JeanRenier/Remoting-a-microBIT-X/pictures/home_receiving.jpg

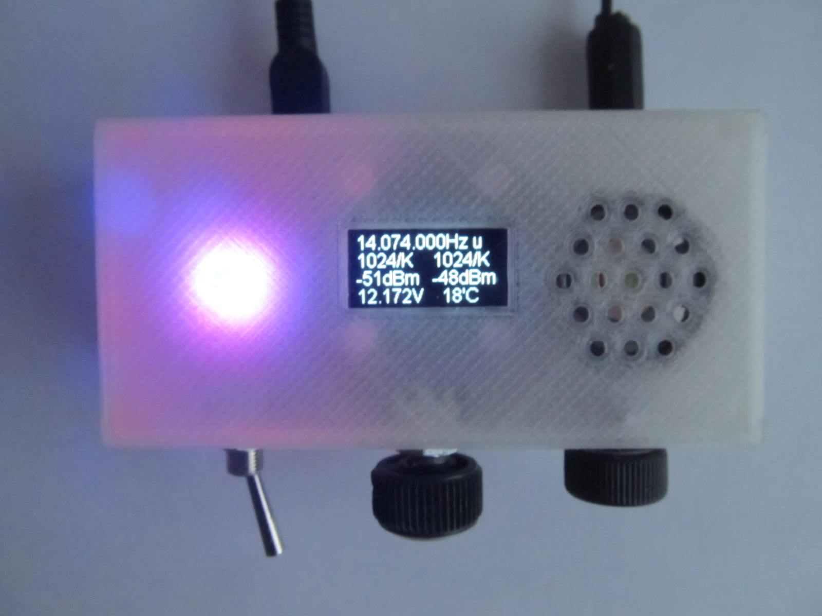
pictures/home_receiving.jpg
