JeanRenier/Remoting-a-microBIT-X/pictures/remote_housing.jpg

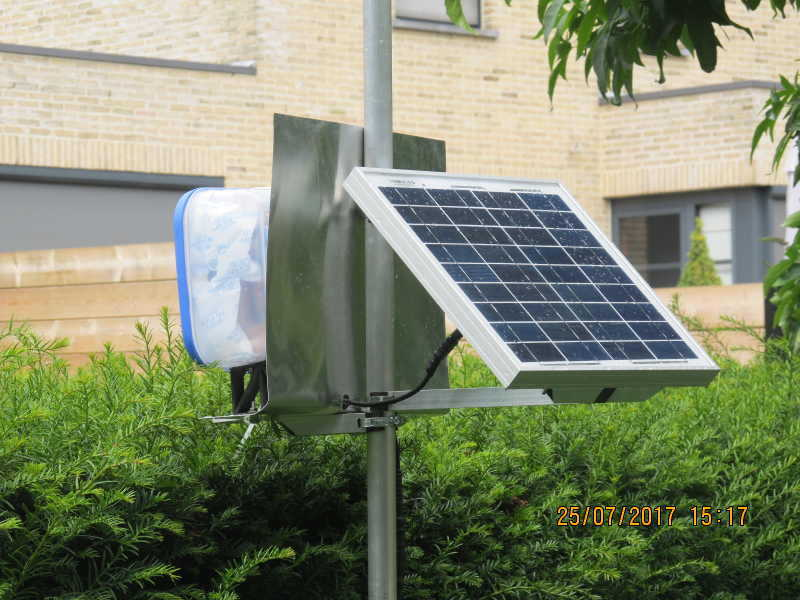
pictures/remote_housing.jpg
