JeanRenier/Remoting-a-microBIT-X/pictures/remote_WiFi_antenna.jpg

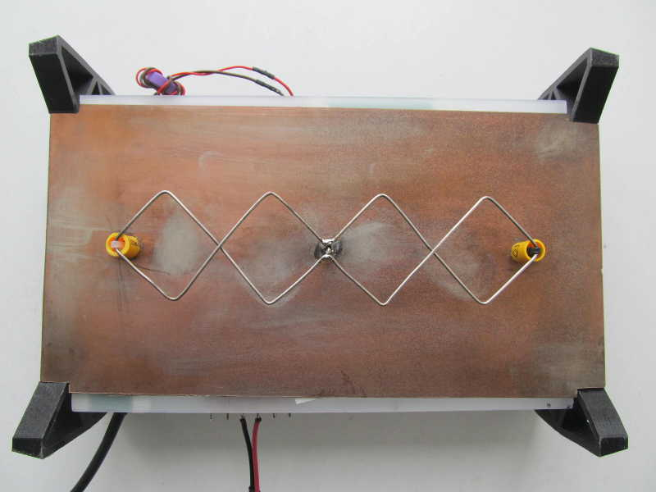
pictures/remote_WiFi_antenna.jpg
