JeanRenier/Remoting-a-microBIT-X/pictures/WSJT-X_gridtracker.png

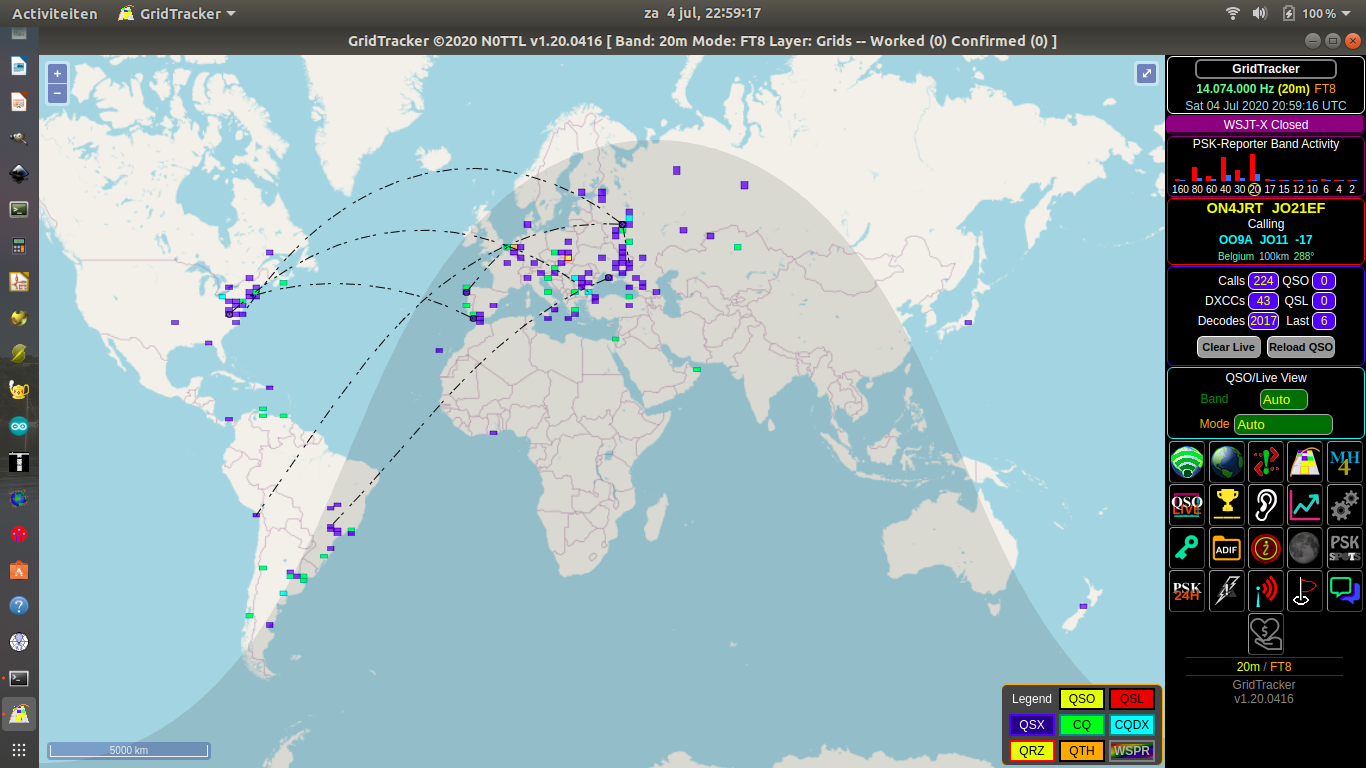
pictures/WSJT-X_gridtracker.png
