JeanRenier/Remoting-a-microBIT-X/pictures/WSJT-X_QSO.png

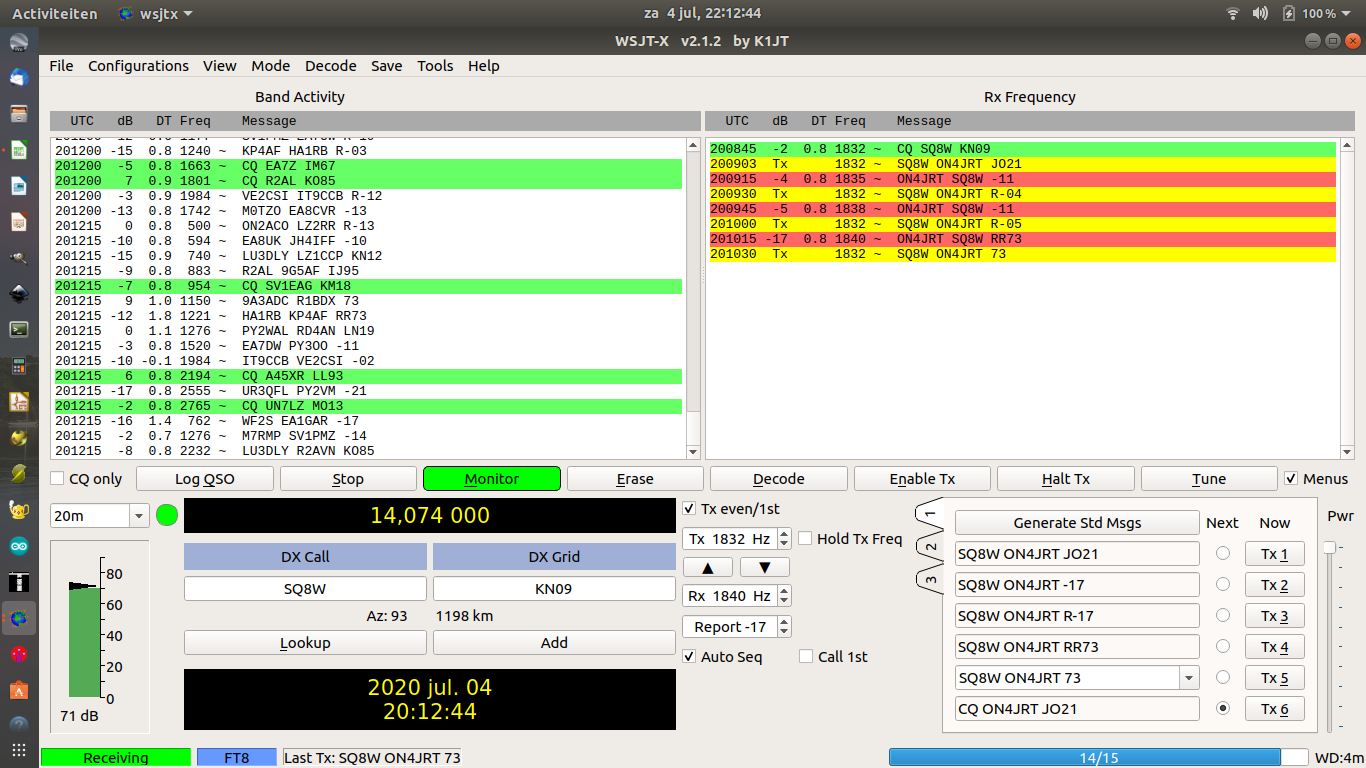
pictures/WSJT-X_QSO.png
