JeanRenier/Remoting-a-microBIT-X/solarCtl/solar_ctl_layout.png

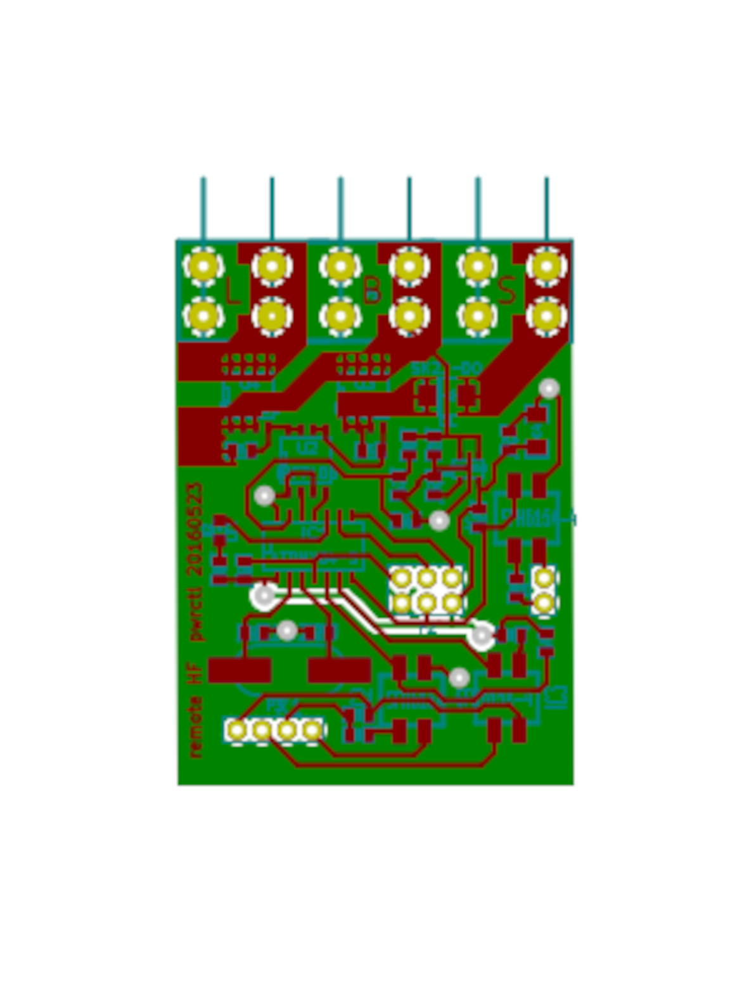
solarCtl/solar_ctl_layout.png
